pulse89/H-Shifter/3D Files/STEP/Shifter Knob.STEP

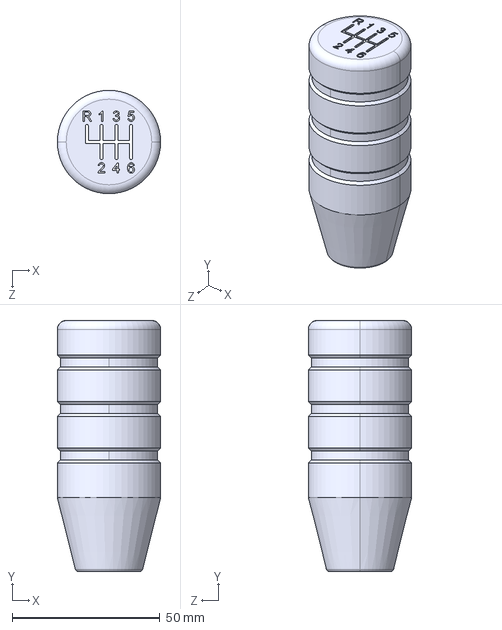
[picture p16: CAD file, 2025-01-30]
3D Files/STEP/Shifter Knob.STEP
35.0 x 85.0 x 35.0 mm
