pulse89/H-Shifter/3D Files/STEP/Spring Tensioner.STEP

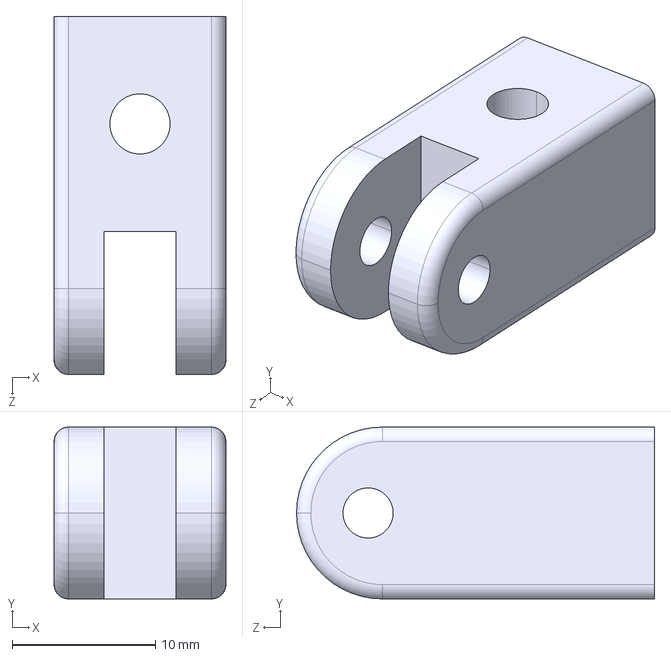
[picture p17: CAD file, 2025-01-30]
3D Files/STEP/Spring Tensioner.STEP
12.0 x 12.0 x 25.0 mm
