pulse89/H-Shifter/3D Files/SW/Shaft Pivot.SLDPRT

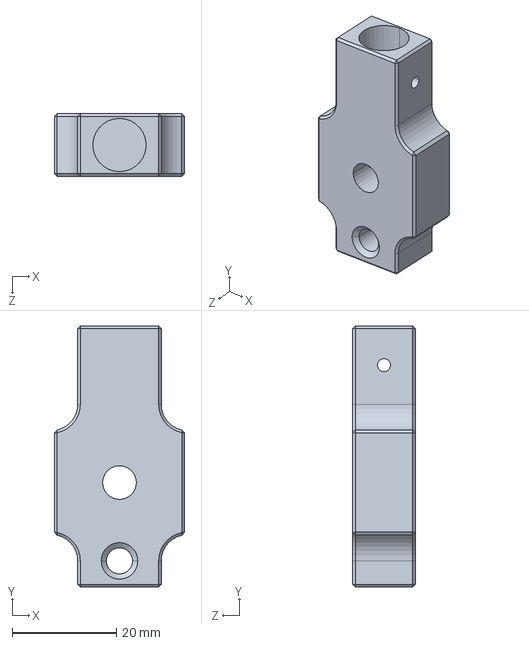
[picture p18: CAD file, 2025-03-25]
3D Files/SW/Shaft Pivot.SLDPRT
25.0 x 50.0 x 12.0 mm
