pulse89/H-Shifter/3D Files/STEP/Shifter Spring End Plate.STEP

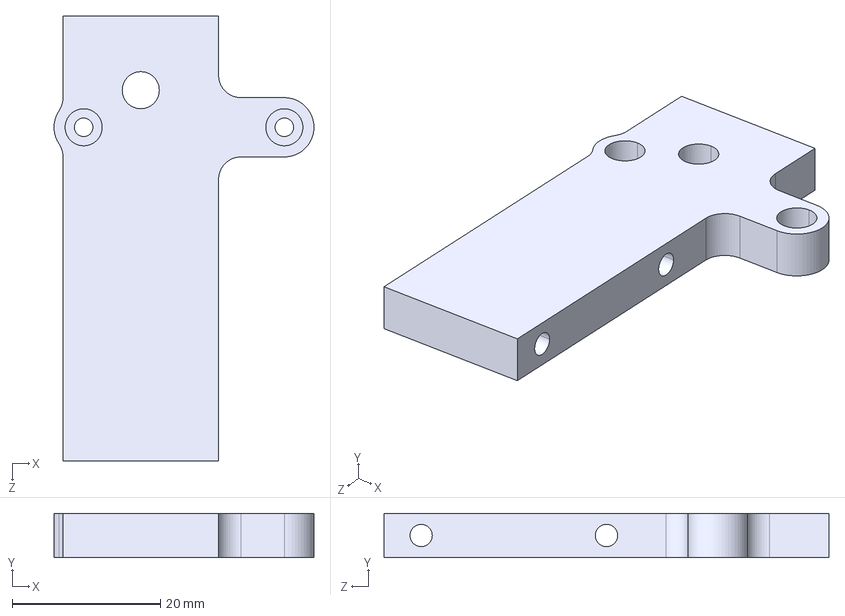
[picture p19: CAD file, 2025-01-30]
3D Files/STEP/Shifter Spring End Plate.STEP
35.1 x 6.00 x 60.0 mm
