pulse89/H-Shifter/3D Files/STL/Printed Bearing Block.STL

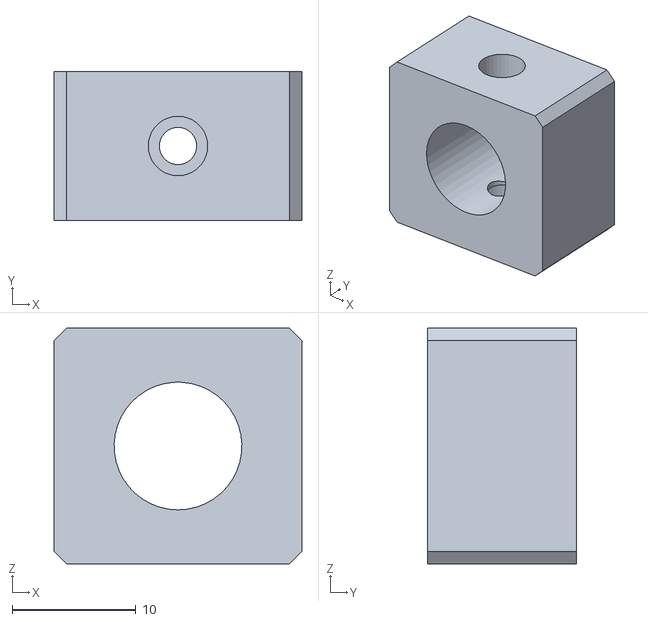
[picture p20: CAD file, 2025-01-30]
3D Files/STL/Printed Bearing Block.STL
20.0 x 12.0 x 19.0
