pulse89/H-Shifter/3D Files/STEP/Shifter End Plate.STEP

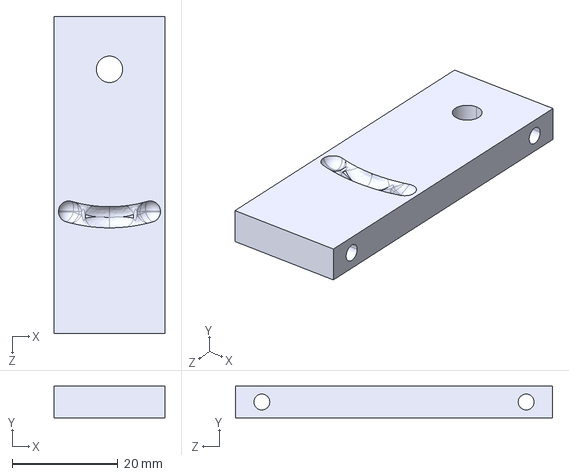
[picture p21: CAD file, 2025-01-30]
3D Files/STEP/Shifter End Plate.STEP
21.0 x 6.00 x 60.0 mm
