pulse89/H-Shifter/3D Files/STL/PETG Bushing.STL

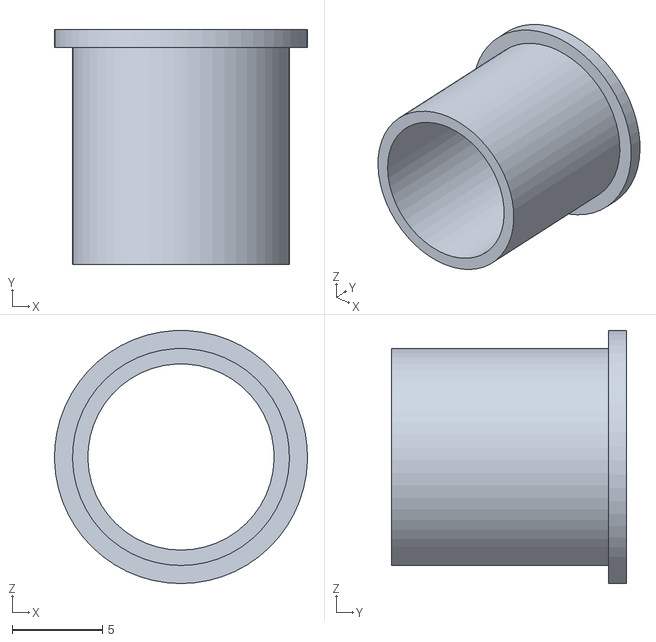
[picture p22: CAD file, 2025-01-30]
3D Files/STL/PETG Bushing.STL
14.0 x 13.0 x 14.0
