pulse89/H-Shifter/3D Files/SW/Shifter Spring.SLDPRT

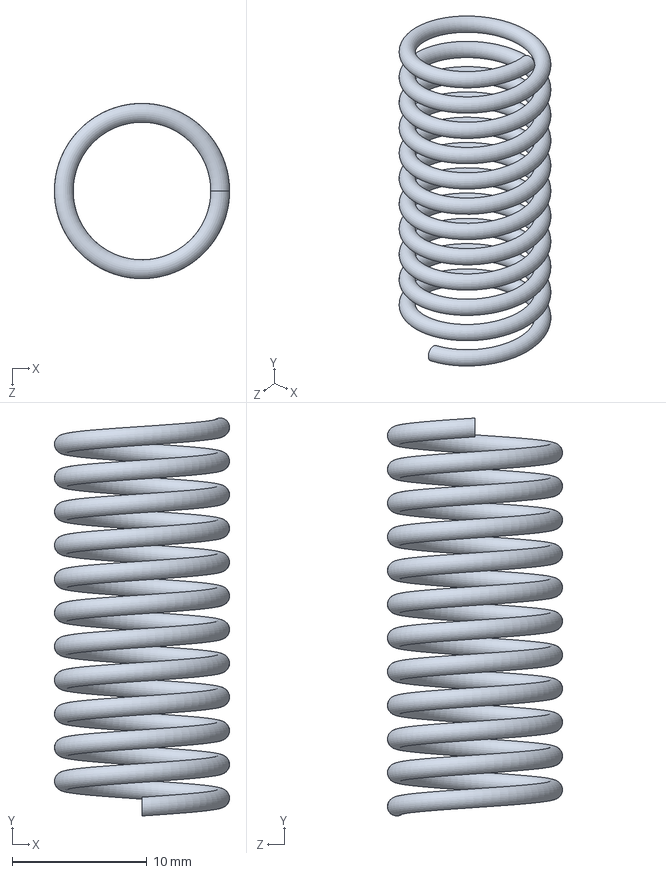
[picture p23: CAD file, 2025-03-24]
3D Files/SW/Shifter Spring.SLDPRT
13.0 x 29.5 x 13.0 mm
