pulse89/H-Shifter/3D Files/STEP/Housing Front.STEP

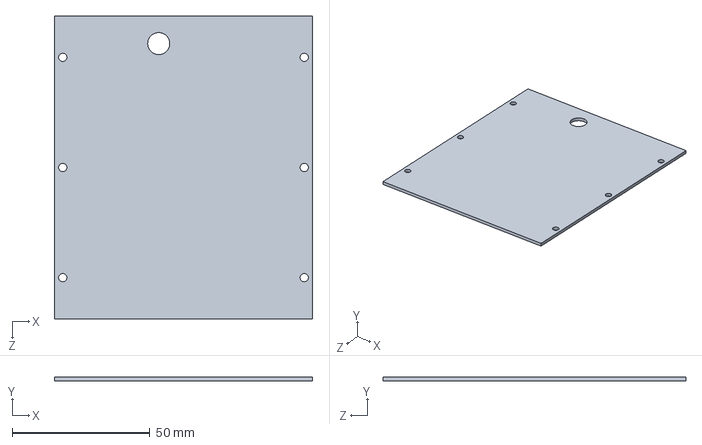
[picture p24: CAD file, 2025-01-30]
3D Files/STEP/Housing Front.STEP
93.7 x 1.50 x 110.0 mm
