pulse89/H-Shifter/3D Files/SW/R4ZZ Bearing.SLDPRT

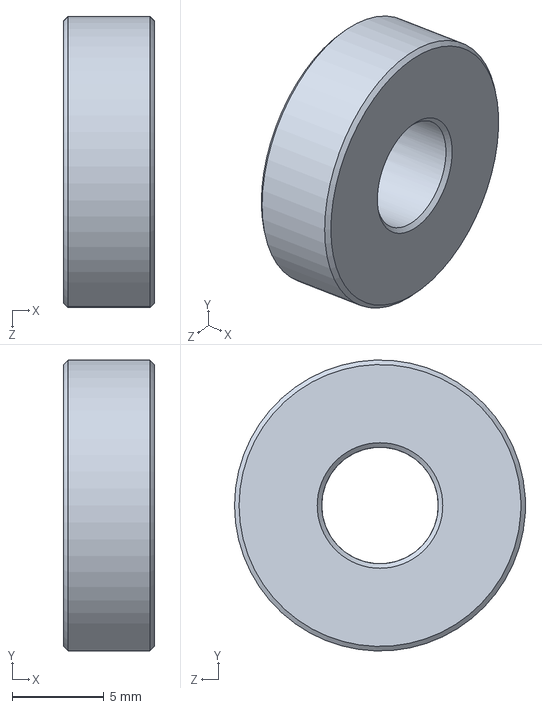
[picture p25: CAD file, 2025-03-24]
3D Files/SW/R4ZZ Bearing.SLDPRT
4.98 x 15.9 x 15.9 mm
