pulse89/H-Shifter/3D Files/SW/Shifter Side Plate 2.SLDPRT

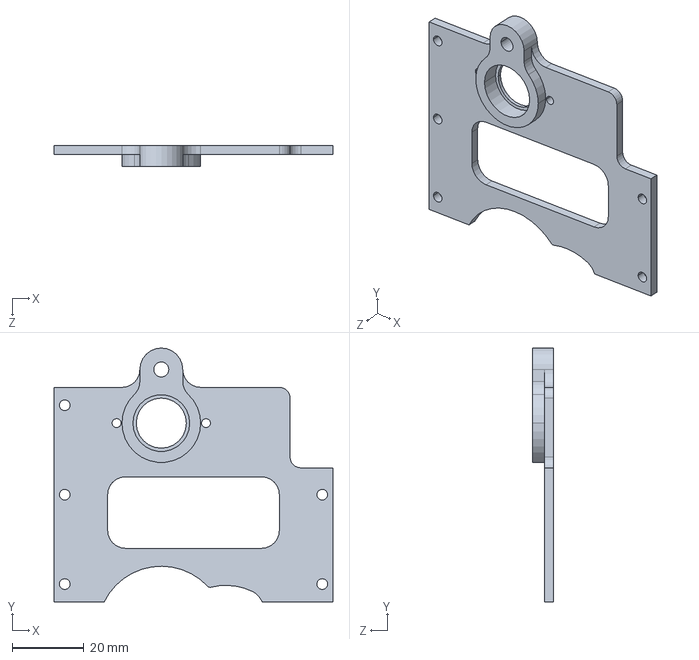
[picture p26: CAD file, 2025-03-24]
3D Files/SW/Shifter Side Plate 2.SLDPRT
78.0 x 71.0 x 6.00 mm
