pulse89/H-Shifter/3D Files/STEP/Desk Mount.STEP

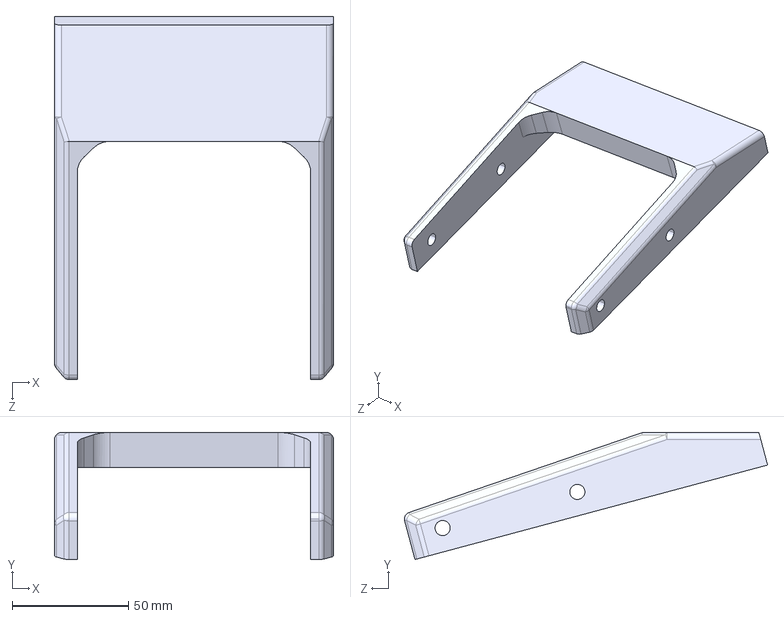
[picture p27: CAD file, 2025-01-30]
3D Files/STEP/Desk Mount.STEP
120.0 x 54.6 x 156.2 mm
