pulse89/H-Shifter/3D Files/SW/623 Bearing.SLDPRT

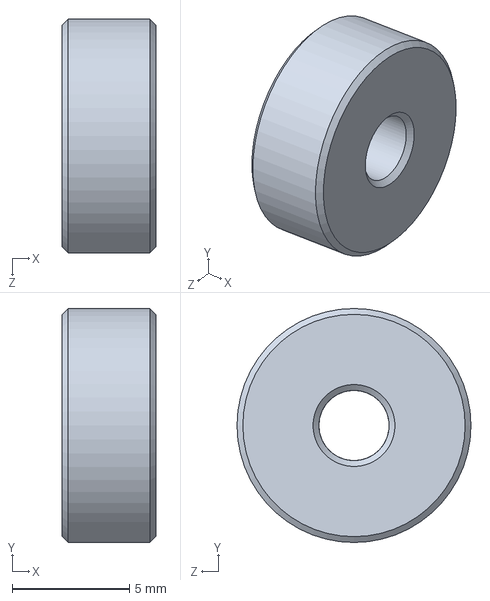
[picture p28: CAD file, 2025-03-24]
3D Files/SW/623 Bearing.SLDPRT
4.00 x 10.0 x 10.0 mm
