pulse89/H-Shifter/3D Files/SW/Shaft.SLDPRT

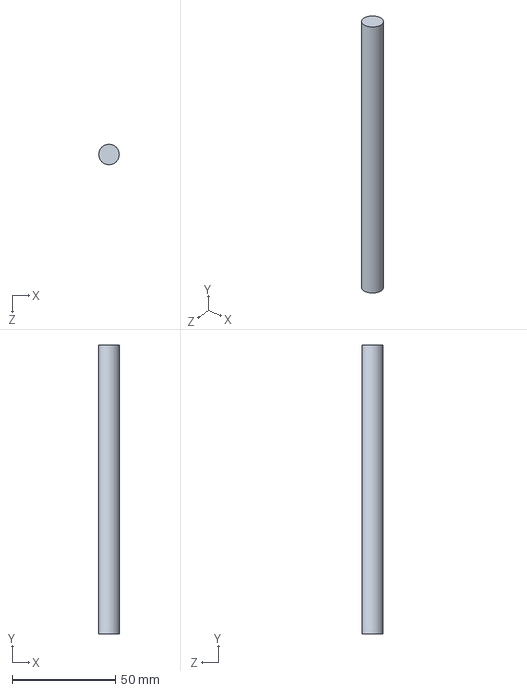
[picture p29: CAD file, 2025-03-24]
3D Files/SW/Shaft.SLDPRT
10.0 x 140.0 x 10.0 mm
