pulse89/H-Shifter/3D Files/SW/R1212N_D-Shaft.SLDPRT

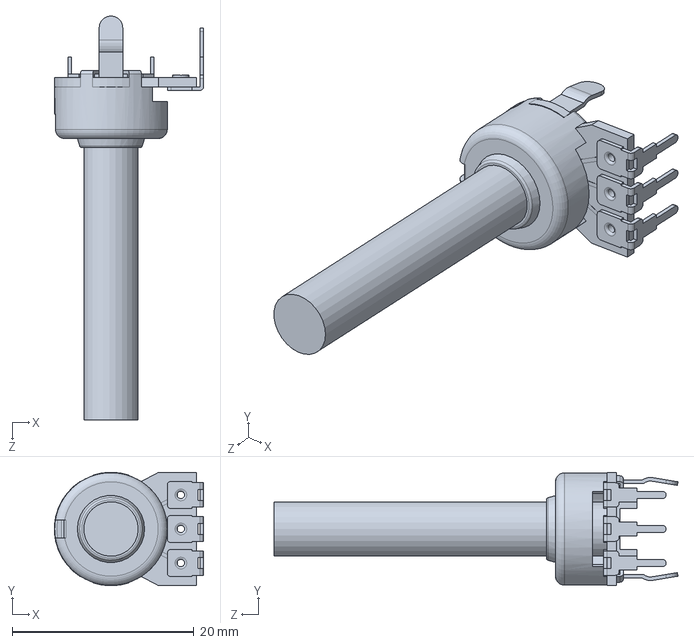
[picture p30: CAD file, 2025-03-24]
3D Files/SW/R1212N_D-Shaft.SLDPRT
16.4 x 12.5 x 44.5 mm
